Plastic-Scanner/handheld-scanner/CAD/Physical design/Old/Solidworks/USB gasket.SLDPRT

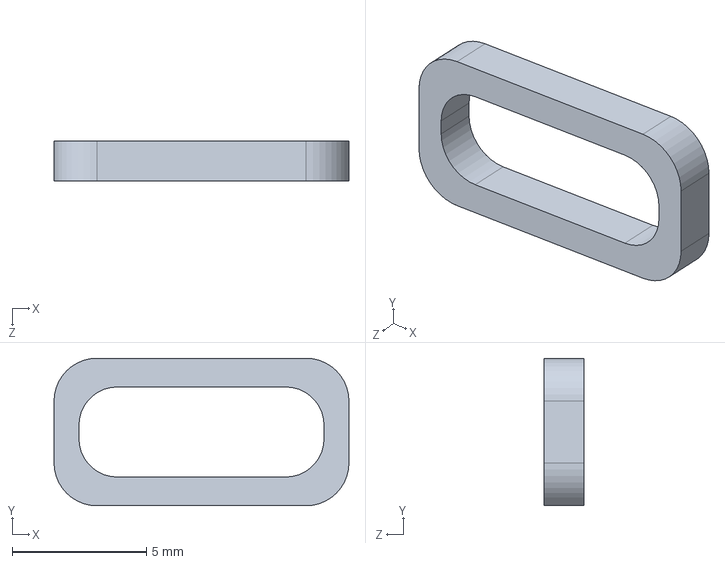
[picture p22: CAD file, 2022-12-23, an earlier design]
CAD/Physical design/Old/Solidworks/USB gasket.SLDPRT
11.0 x 5.50 x 1.50 mm
