Plastic-Scanner/handheld-scanner/Firmware/Arduino/PlasticScannerToSheets/PlasticScannerToSheets.ino

 
#ifdef ESP32
  #include <WiFi.h>
#else
  #include <ESP8266WiFi.h>
#endif


/////////////////////////////////////////////////////////////////////////
//      Google sheets setup


// Replace with your SSID and Password
const char* ssid     = "Markus - iPhone";
const char* password = "TakForNetDu";

//const char* ssid     = "Hvilehjemsvej 38";
//const char* password = "20870729";


// Replace with your unique IFTTT URL resource
const char* resource = "/trigger/PlasticScanned/with/key/bl96IM25tg14213NBlSzwH";

// How your resource variable should look like, but with your own API KEY (that API KEY below is just an example):
//const char* resource = "/trigger/bme280_readings/with/key/nAZjOphL3d-ZO4N3k64-1A7gTlNSrxMJdmqy3";

// Maker Webhooks IFTTT
const char* server = "maker.ifttt.com";

float Reading1 = 0;
float Reading2 = 0;
float Reading3 = 0;
float Reading4 = 0;
float Reading5 = 0;
float Reading6 = 0;
float Reading7 = 0;
float Reading8 = 0;



// Time to sleep
uint64_t uS_TO_S_FACTOR = 1000000;  // Conversion factor for micro seconds to seconds
// sleep for 3 minutes = 180 seconds
uint64_t TIME_TO_SLEEP = 30;

/////////////////////////////////////////////////////////////////////////






void setup() {
  Serial.begin(115200); 
  delay(2000);


  initWifi();
  makeIFTTTRequest();
    
  #ifdef ESP32

    delay(10000);
    // enable timer deep sleep
    esp_sleep_enable_timer_wakeup(TIME_TO_SLEEP * uS_TO_S_FACTOR);    
    Serial.println("Going to sleep now");
    // start deep sleep for 3600 seconds (60 minutes)
    esp_deep_sleep_start();

  #endif
}

void loop() {
  // Her skal der være noget der gør at den bare venter

}

// Establish a Wi-Fi connection with your router
void initWifi() {
  Serial.print("Connecting to: "); 
  Serial.print(ssid);
  WiFi.begin(ssid, password);  

  int timeout = 10 * 4; // 10 seconds
  while(WiFi.status() != WL_CONNECTED  && (timeout-- > 0)) {
    delay(250);
    Serial.print(".");
  }
  Serial.println("");

  if(WiFi.status() != WL_CONNECTED) {
     Serial.println("Failed to connect, going back to sleep");
  }

  Serial.print("WiFi connected in: "); 
  Serial.print(millis());
  Serial.print(", IP address: "); 
  Serial.println(WiFi.localIP());
}

// Make an HTTP request to the IFTTT web service
void makeIFTTTRequest() {
  Serial.print("Connecting to "); 
  Serial.print(server);
  
  WiFiClient client;
  int retries = 5;
  while(!!!client.connect(server, 80) && (retries-- > 0)) {
    Serial.print(".");
  }
  Serial.println();
  if(!!!client.connected()) {
    Serial.println("Failed to connect...");
  }
  
  Serial.print("Request resource: "); 
  Serial.println(resource);

  // Temperature in Celsius
  String jsonObject = String("{\"value1\":\"") + Reading1 + ";" + Reading2 + ";" + Reading3  + "\"}";
                      
  // Comment the previous line and uncomment the next line to publish temperature readings in Fahrenheit                    
  /*String jsonObject = String("{\"value1\":\"") + (1.8 * bme.readTemperature() + 32) + "\",\"value2\":\"" 
                      + (bme.readPressure()/100.0F) + "\",\"value3\":\"" + bme.readHumidity() + "\"}";*/
                      
  client.println(String("POST ") + resource + " HTTP/1.1");
  client.println(String("Host: ") + server); 
  client.println("Connection: close\r\nContent-Type: application/json");
  client.print("Content-Length: ");
  client.println(jsonObject.length());
  client.println();
  client.println(jsonObject);
        
  int timeout = 5 * 10; // 5 seconds             
  while(!!!client.available() && (timeout-- > 0)){
    delay(100);
  }
  if(!!!client.available()) {
    Serial.println("No response...");
  }
  while(client.available()){
    Serial.write(client.read());
  }
  
  Serial.println("\nclosing connection");
  client.stop(); 
}
